DanyYanev/Laufdaten.info-Indoor-Display/shields/Indoor Display Shield/Lcd 2.80/Pictures ESP-12E/Two buttons2.jpg

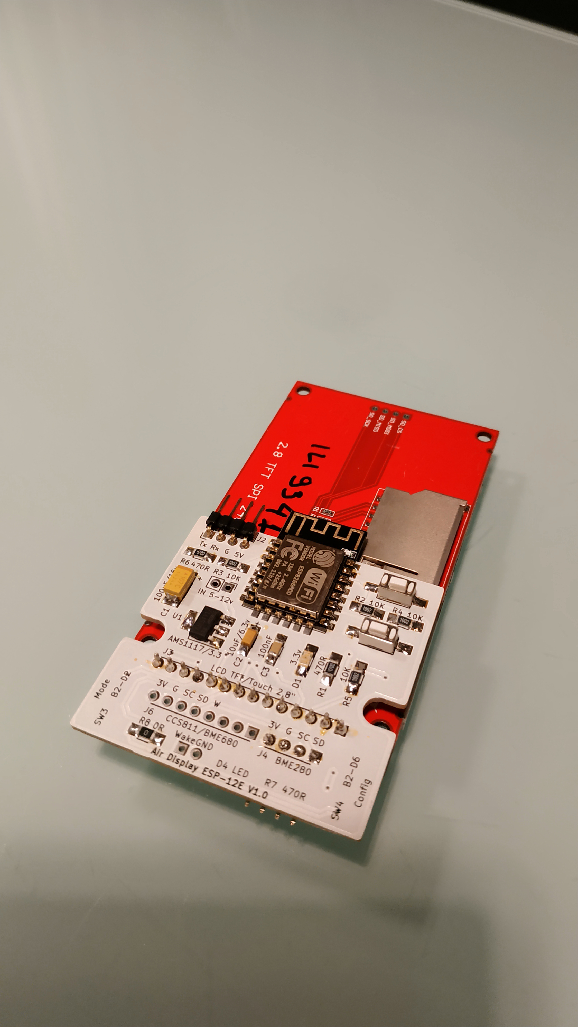
shields/Indoor Display Shield/Lcd 2.80/Pictures ESP-12E/Two buttons2.jpg
