DanyYanev/Laufdaten.info-Indoor-Display/shields/Indoor Display Shield/Oled/Pictures/20180408_222358.jpg

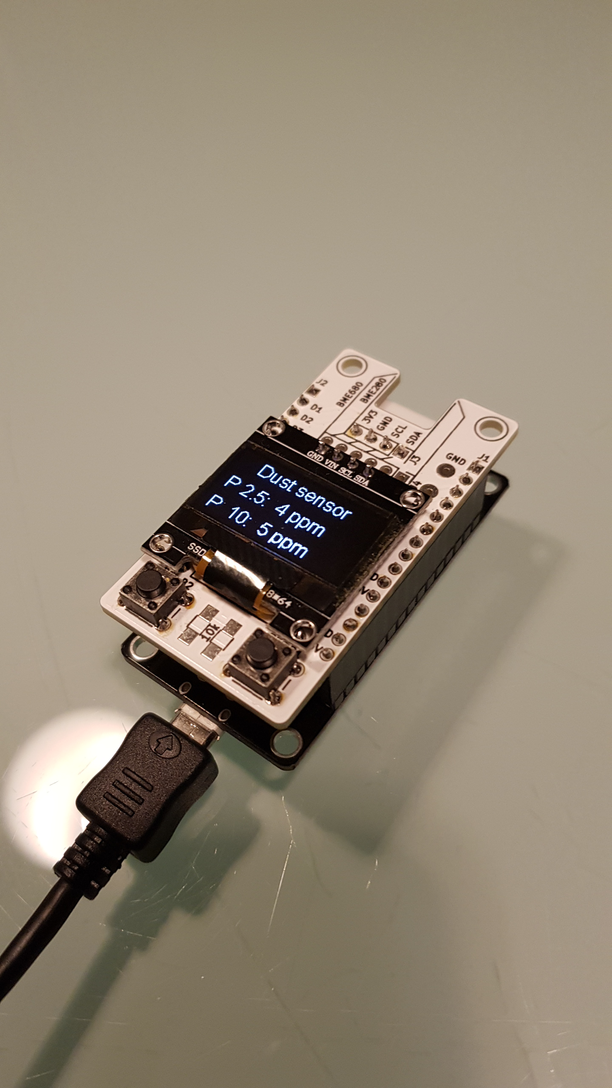
shields/Indoor Display Shield/Oled/Pictures/20180408_222358.jpg
