DanyYanev/Laufdaten.info-Indoor-Display/shields/Outdoor Sensor Shield/Pictures/20180309_204832.jpg

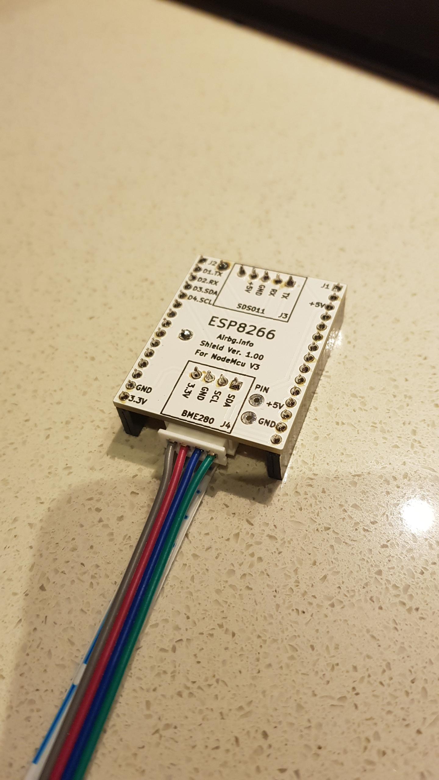
shields/Outdoor Sensor Shield/Pictures/20180309_204832.jpg
